silvioviscuso/ESP32-REACTJS-DEVKIT/Assets/1.png

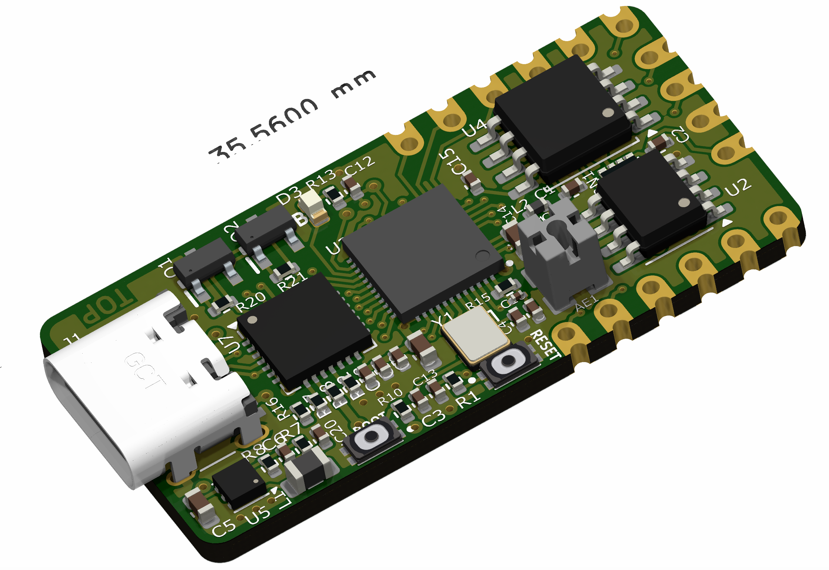
Assets/1.png
