silvioviscuso/ESP32-REACTJS-DEVKIT/Assets/Preview 2024-11-06 alle 11.11.40.png

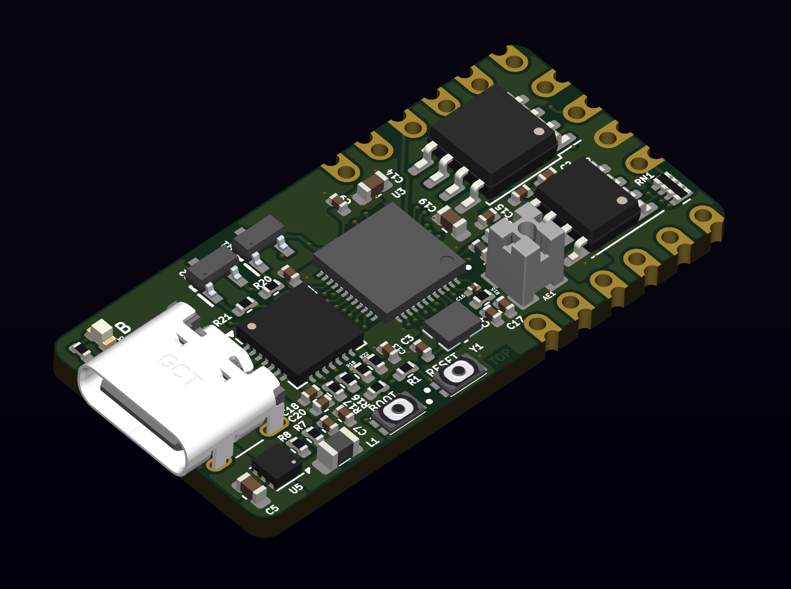
Assets/Preview 2024-11-06 alle 11.11.40.png
