silvioviscuso/ESP32-REACTJS-DEVKIT/Production data/PDF3D/V1.png

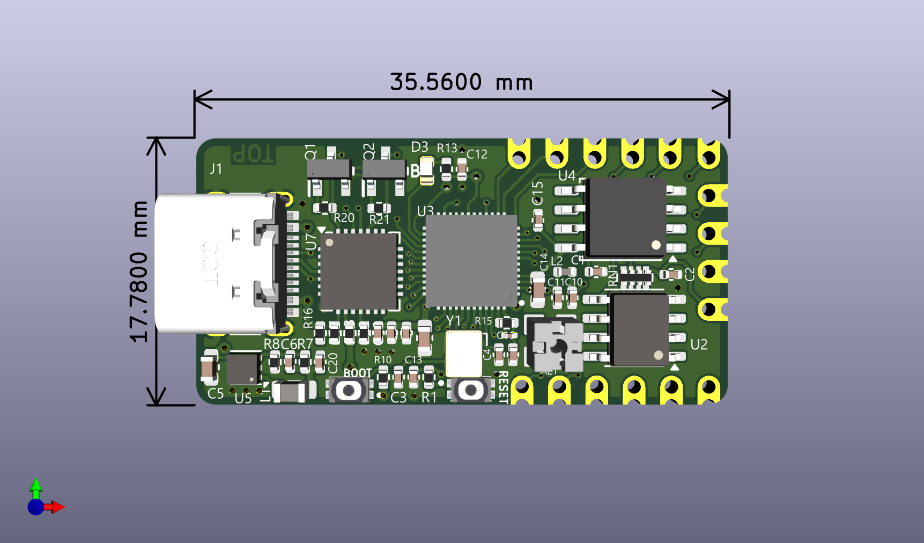
Production data/PDF3D/V1.png
