silvioviscuso/ESP32-REACTJS-DEVKIT/Production data/PDF3D/V1_back.png

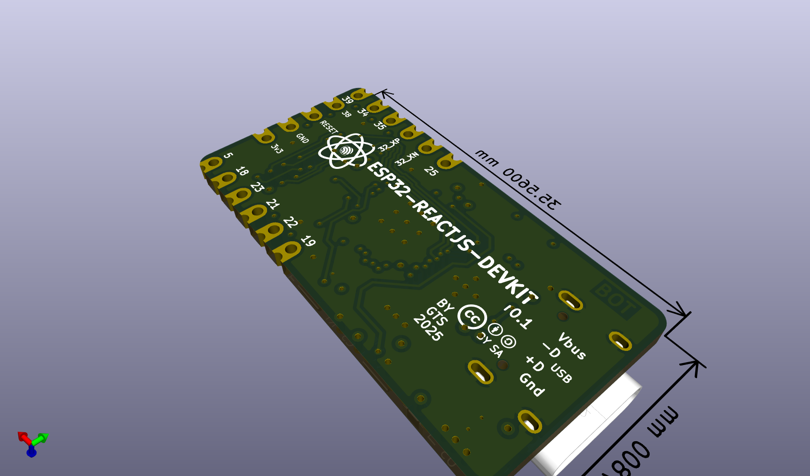
Production data/PDF3D/V1_back.png
