silvioviscuso/ESP32-REACTJS-DEVKIT/ESP32-DOWDQ6-16MB-BOILERPLATE-SCH/Boilerplate_esp-dowdq6_sch/Boilerplate_esp-dowdq6_sch.kicad_sch

## KiCad design ESP32-DOWDQ6-16MB-BOILERPLATE-SCH/Boilerplate_esp-dowdq6_sch/Boilerplate_esp-dowdq6_sch.kicad_sch (2024-12-04)

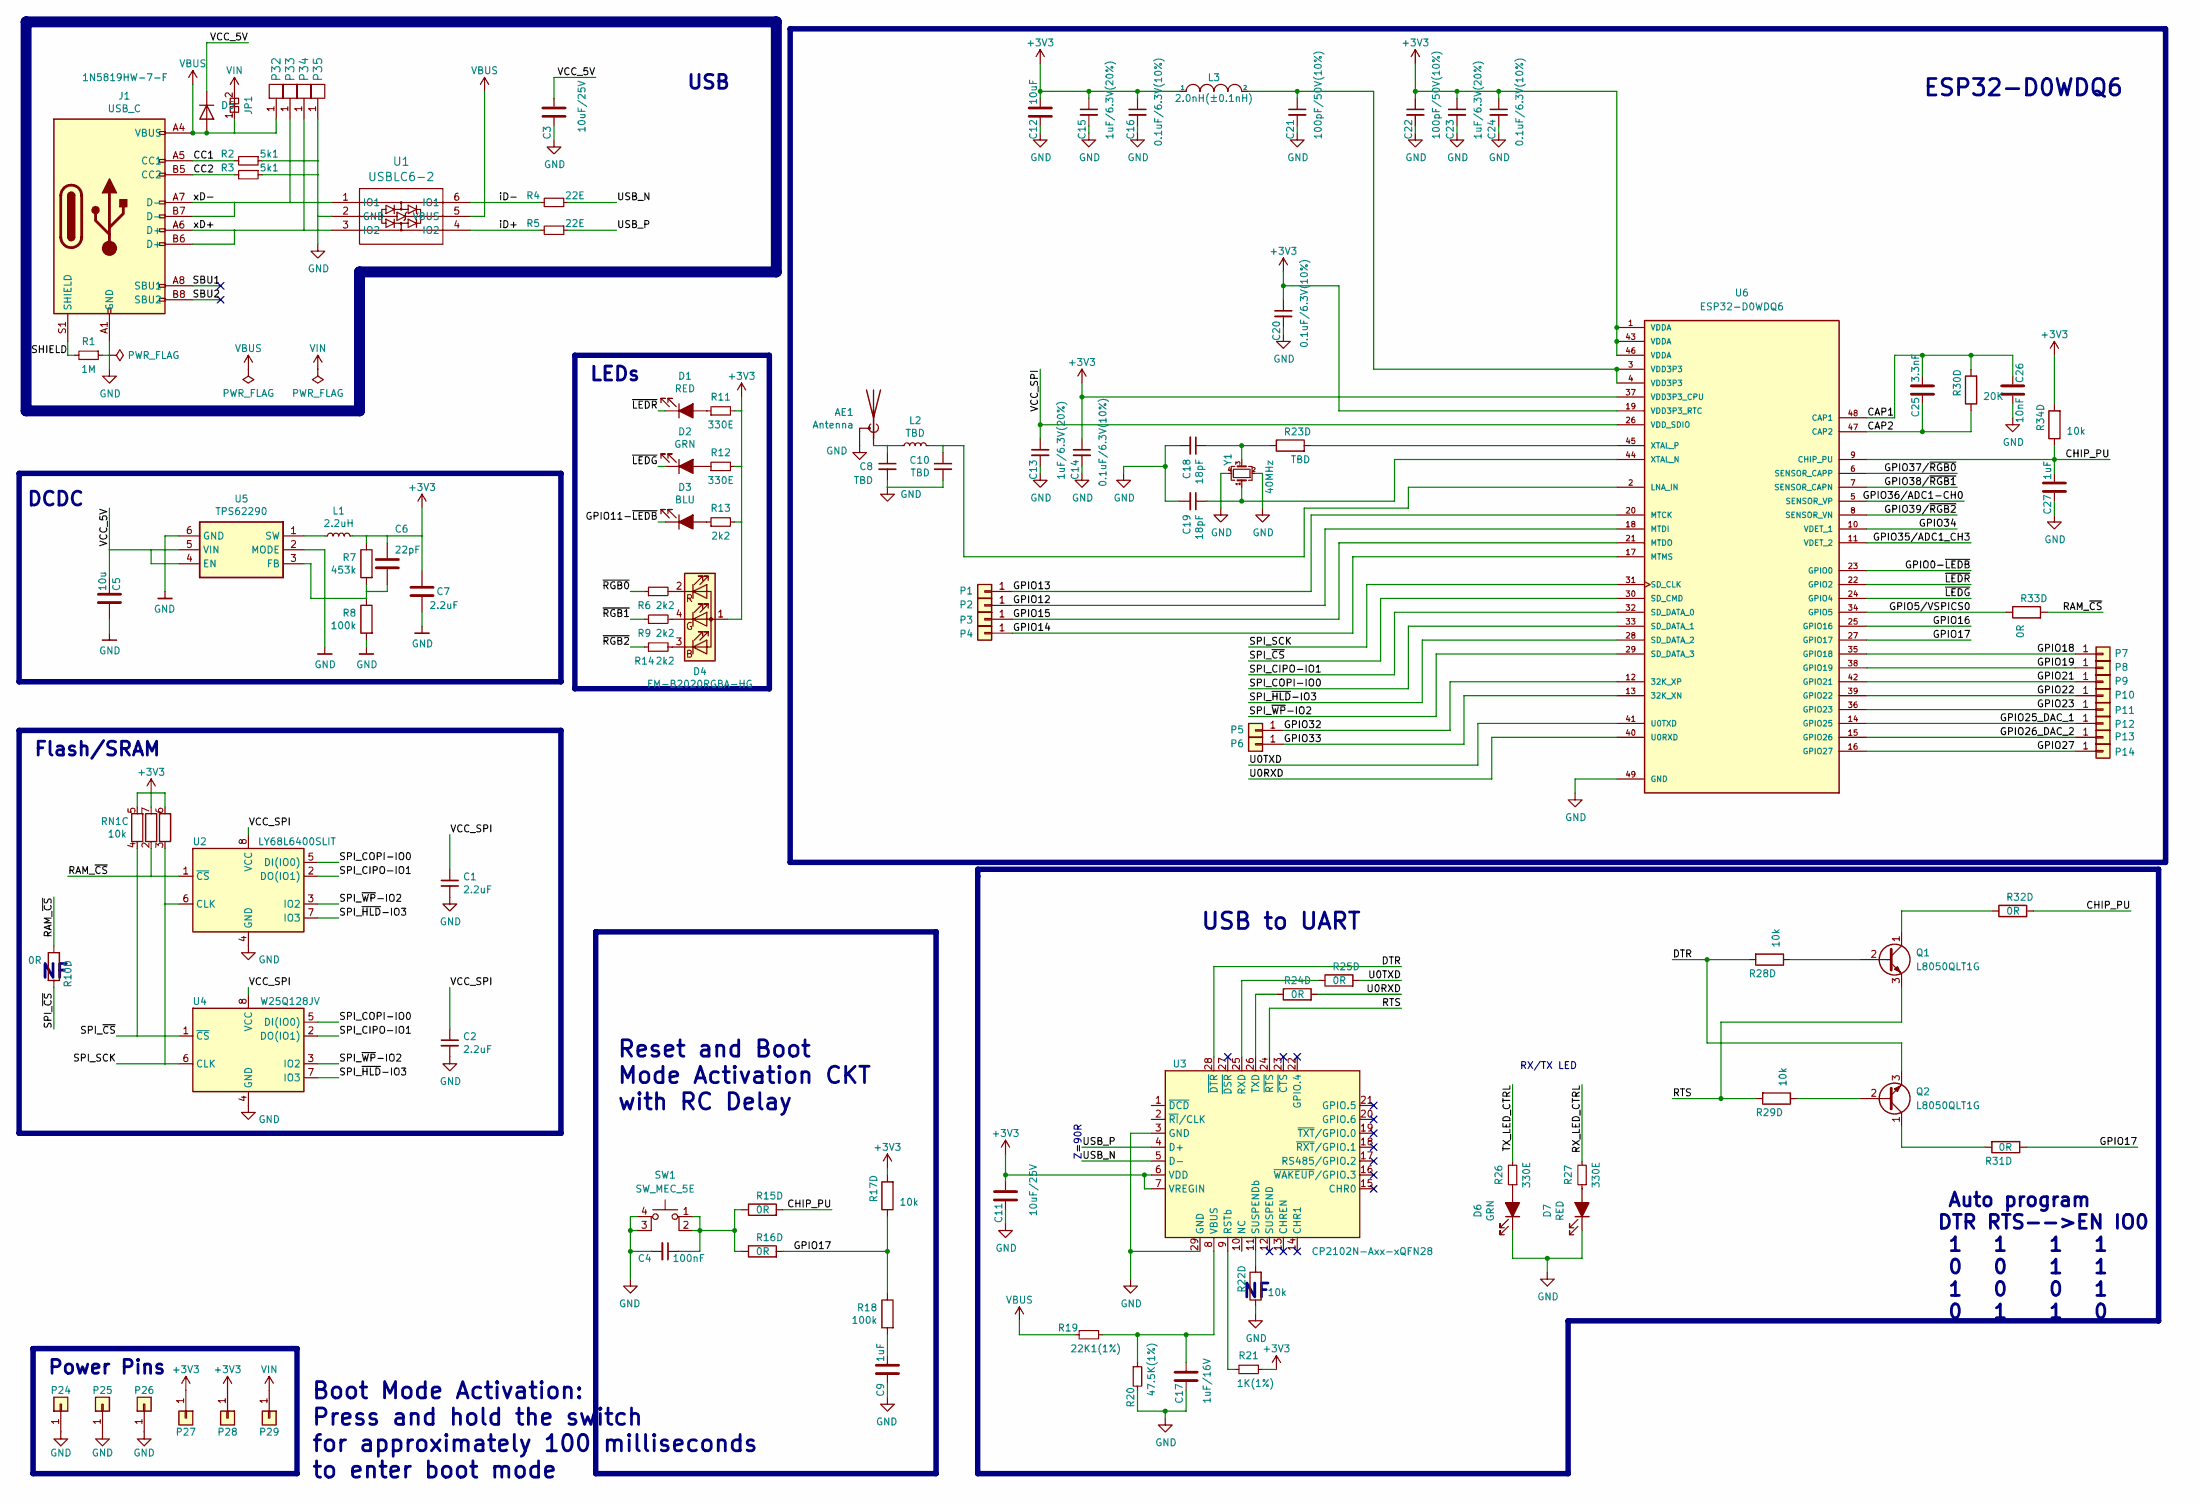
[picture p29: schematic Boilerplate_esp-dowdq6_sch.kicad_sch]

Parts:
AE1: Antenna; 0479480001
C1, C2, C7: 2.2uF; C_0402_1005Metric
C3, C11: 10uF/25V; C_0603_1608Metric
C4: 100nF; C_0402_1005Metric
C5: 10u; C_0603_1608Metric
C6: 22pF; C_0402_1005Metric
C8, C10: TBD; C_0402_1005Metric
C9, C27: 1uF; C_0603_1608Metric
C12: 10uF; C_0603_1608Metric
C13, C15, C23: 1uF/6.3V(20%); C_0402_1005Metric
C14, C16, C20, C24: 0.1uF/6.3V(10%); C_0402_1005Metric
C17: 1uF/16V; C_0603_1608Metric
C18, C19: 18pF; C_0402_1005Metric
C21, C22: 100pF/50V(10%); C_0402_1005Metric
C25: 3.3nF; C_0603_1608Metric
C26: 10nF; C_0603_1608Metric
D1, D7: RED; LED_0603_1608Metric_Compact
D2, D6: GRN; LED_0603_1608Metric_Compact
D3: BLU; LED_0603_1608Metric_Compact
D4: FM-B2020RGBA-HG; LED_Lumex_SML-LX0303SIUPGUSB
D5: 1N5819HW-7-F; D_SOD-123
J1: USB_C; USB_C_Receptacle_HRO_TYPE-C-31-M-12
JP1: Jumper; SolderJumper-2_P1.3mm_Bridged2Bar_RoundedPad1.0x1.5mm
L1: 2.2uH; L_0805_2012Metric
L2: TBD; L_0402_1005Metric
L3: 2.0nH(±0.1nH); L_0402_1005Metric
P1: 4; Pin_Header_Straight_Round_1x01_Castellated
P2: 5; Pin_Header_Straight_Round_1x01_Castellated
P3: 6; Pin_Header_Straight_Round_1x01_Castellated
P4: 7; Pin_Header_Straight_Round_1x01_Castellated
P5: 20; Pin_Header_Straight_Round_1x01_Castellated
P6: 21; Pin_Header_Straight_Round_1x01_Castellated
P7: 3; Pin_Header_Straight_Round_1x01_Castellated
P8: 1; Pin_Header_Straight_Round_1x01_Castellated
P9: 0; Pin_Header_Straight_Round_1x01_Castellated
P10: 2; Pin_Header_Straight_Round_1x01_Castellated
P11: 8; Pin_Header_Straight_Round_1x01_Castellated
P12: 10; Pin_Header_Straight_Round_1x01_Castellated
P13: 23; Pin_Header_Straight_Round_1x01_Castellated
P14: 22; Pin_Header_Straight_Round_1x01_Castellated
P24, P25, P26: GND; Pin_Header_Straight_Round_1x01_Castellated
P27, P28: 3V3; Pin_Header_Straight_Round_1x01_Castellated
P29: VIN; Pin_Header_Straight_Round_1x01_Castellated
P32, P33, P34, P35: UP; PAD_SMD_1x2.65_ROUNDED
Q1, Q2: L8050QLT1G; TO-92_Inline
R1: 1M; R_0402_1005Metric
R2, R3: 5k1; R_0402_1005Metric
R4, R5: 22E; R_0402_1005Metric
R6, R9, R13, R14: 2k2; R_0402_1005Metric
R7: 453k; R_0402_1005Metric
R8, R18: 100k; R_0402_1005Metric
R10, R15, R16, R24, R25, R31, R32, R33: 0R; R_0402_1005Metric
R11, R12, R26, R27: 330E; R_0402_1005Metric
R17, R22, R28, R29, R34: 10k; R_0402_1005Metric
R19: 22K1(1%); R_0603_1608Metric
R20: 47.5K(1%); R_0402_1005Metric
R21: 1K(1%); R_0402_1005Metric
R23: TBD; R_0402_1005Metric
R30: 20K; R_0402_1005Metric
RN1: 10k; R_0402_1005Metric
SW1: SW_MEC_5E; SW_Push_1P1T_NO_6x6mm_H9.5mm
U1: USBLC6-2; SOT-666
U2: LY68L6400SLIT; SOIC-8_3.9x4.9mm_P1.27mm
U3: CP2102N-Axx-xQFN28; QFN-28-1EP_5x5mm_P0.5mm_EP3.35x3.35mm
U4: W25Q128JV; SOIC-8_5.23x5.23mm_P1.27mm
U5: TPS62290; WSON-6-1EP_2x2mm_P0.65mm_EP1x1.6mm_ThermalVias
U6: ESP32-D0WDQ6
Y1: 40MHz; Crystal_SMD_Abracon_ABM10-4Pin_2.5x2.0mm

Connections:
+3V3: C6.1, C7.1, C11.1, C12.1, C14.1, C15.1, C16.1, C20.1, C22.1, C23.1, C24.1, D4.1 (A), L1.2, L3.1, P27.1, P28.1, R7.1, R11.2, R12.2, R13.2, R17.5 (R4.2), R21.1, R34.5 (R4.2), RN1.5 (R4.2), RN1.6 (R3.2), RN1.7 (R2.2), U3.6 (VDD), U3.7 (VREGIN), U6.1 (VDDA), U6.19 (VDD3P3_RTC), U6.37 (VDD3P3_CPU), U6.43 (VDDA), U6.46 (VDDA)
CAP1: C25.1, C26.2, R30.5 (R4.2), U6.48 (CAP1)
CAP2: C25.2, R30.4 (R4.1), U6.47 (CAP2)
CC1: J1.A5 (CC1), R2.2
CC2: J1.B5 (CC2), R3.2
CHIP_PU: C27.1, R15.5 (R4.2), R32.5 (R4.2), R34.4 (R4.1), U6.9 (CHIP_PU)
DTR: Q2.3 (E), R28.5 (R4.2), U3.28 (~DTR)
GND: AE1.2 (Shield), C1.2, C2.2, C3.2, C4.2, C5.2, C7.2, C8.2, C9.2, C10.2, C11.2, C12.2, C13.2, C14.2, C15.2, C16.2, C17.2, C18.2, C19.2, C20.2, C21.2, C22.2, C23.2, C24.2, C26.1, C27.2, D6.1 (K), D7.1 (K), J1.A1 (GND), J1.A12 (GND), J1.B1 (GND), J1.B12 (GND), P24.1, P25.1, P26.1, P35.1, R1.1, R2.1, R3.1, R8.2, R20.2, R22.4 (R4.1), SW1.3 (K), SW1.4 (A), U1.2 (GND), U2.4 (GND), U3.3 (GND), U3.29 (GND), U4.4 (GND), U5.2 (MODE), U5.6 (GND), U5.7 (GND), U6.49 (GND), Y1.2, Y1.4
GPIO0-~LEDB: U6.23 (GPIO0)
GPIO5/VSPICS0: R33.4 (R4.1), U6.34 (GPIO5)
GPIO11-~LEDB: D3.1 (K)
GPIO12: P2.1, U6.18 (MTDI)
GPIO13: P1.1, U6.20 (MTCK)
GPIO14: P4.1, U6.17 (MTMS)
GPIO15: P3.1, U6.21 (MTDO)
GPIO16: U6.25 (GPIO16)
GPIO17: R16.5 (R4.2), R17.4 (R4.1), R18.1, R31.4 (R4.1), U6.27 (GPIO17)
GPIO18: P7.1, U6.35 (GPIO18)
GPIO19: P8.1, U6.38 (GPIO19)
GPIO21: P9.1, U6.42 (GPIO21)
GPIO22: P10.1, U6.39 (GPIO22)
GPIO23: P11.1, U6.36 (GPIO23)
GPIO25_DAC_1: P12.1, U6.14 (GPIO25)
GPIO26_DAC_2: P13.1, U6.15 (GPIO26)
GPIO27: P14.1, U6.16 (GPIO27)
GPIO32: P5.1, U6.12 (32K_XP)
GPIO33: P6.1, U6.13 (32K_XN)
GPIO34: U6.10 (VDET_1)
GPIO35/ADC1_CH3: U6.11 (VDET_2)
GPIO36/ADC1-CH0: U6.5 (SENSOR_VP)
GPIO37/~RGB0: U6.6 (SENSOR_CAPP)
GPIO38/~RGB1: U6.7 (SENSOR_CAPN)
GPIO39/~RGB2: U6.8 (SENSOR_VN)
unnamed: AE1.1 (A), C8.1, L2.2
unnamed: C4.1, R15.4 (R4.1), R16.4 (R4.1), SW1.1, SW1.2
unnamed: C6.2, R7.2, R8.1, U5.3 (FB)
unnamed: C9.1, R18.2
unnamed: C10.1, L2.1, U6.2 (LNA_IN)
unnamed: C17.1, R19.1, R20.1, U3.8 (VBUS)
unnamed: C18.1, R23.4 (R4.1), Y1.3
unnamed: C19.1, U6.44 (XTAL_N), Y1.1
unnamed: C21.1, L3.2, U6.3 (VDD3P3), U6.4 (VDD3P3)
unnamed: D1.2 (A), R11.1
unnamed: D2.2 (A), R12.1
unnamed: D3.2 (A), R13.1
unnamed: D4.2 (RK), R6.2
unnamed: D4.3 (BK), R14.2
unnamed: D4.4 (GK), R9.2
unnamed: D6.2 (A), R26.1
unnamed: D7.2 (A), R27.1
unnamed: L1.1, U5.1 (SW)
unnamed: Q1.1 (C), R32.4 (R4.1)
unnamed: Q1.2 (B), R28.4 (R4.1)
unnamed: Q2.1 (C), R31.5 (R4.2)
unnamed: Q2.2 (B), R29.4 (R4.1)
unnamed: R21.2, U3.9 (RSTb)
unnamed: R22.5 (R4.2), U3.11 (SUSPENDb)
unnamed: R23.5 (R4.2), U6.45 (XTAL_P)
unnamed: R24.4 (R4.1), U3.26 (TXD)
unnamed: R25.4 (R4.1), U3.25 (RXD)
RAM_~CS: R10.4 (R4.1), R33.5 (R4.2), RN1.2 (R2.1), U2.1 (~CS)
RTS: Q1.3 (E), R29.5 (R4.2), U3.24 (~RTS)
RX_LED_CTRL: R27.2
SBU1: J1.A8 (SBU1)
SBU2: J1.B8 (SBU2)
SHIELD: J1.S1 (SHIELD), R1.2
SPI_CIPO-IO1: U2.2 (DO(IO1)), U4.2 (DO(IO1)), U6.32 (SD_DATA_0)
SPI_COPI-IO0: U2.5 (DI(IO0)), U4.5 (DI(IO0)), U6.33 (SD_DATA_1)
SPI_SCK: RN1.3 (R3.1), U2.6 (CLK), U4.6 (CLK), U6.31 (SD_CLK)
SPI_~CS: R10.5 (R4.2), RN1.4 (R4.1), U4.1 (~CS), U6.30 (SD_CMD)
SPI_~HLD-IO3: U2.7 (IO3), U4.7 (IO3), U6.28 (SD_DATA_2)
SPI_~WP-IO2: U2.3 (IO2), U4.3 (IO2), U6.29 (SD_DATA_3)
TX_LED_CTRL: R26.2
U0RXD: R24.5 (R4.2), U6.40 (U0RXD)
U0TXD: R25.5 (R4.2), U6.41 (U0TXD)
USB_N: R4.1, U3.5 (D-)
USB_P: R5.1, U3.4 (D+)
VBUS: D5.2 (A), J1.A4 (VBUS), J1.A9 (VBUS), J1.B4 (VBUS), J1.B9 (VBUS), JP1.1, P32.1, R19.2, U1.5 (VBUS)
VCC_5V: C3.1, C5.1, D5.1 (K), U5.4 (EN), U5.5 (VIN)
VCC_SPI: C1.1, C2.1, C13.1, U2.8 (VCC), U4.8 (VCC), U6.26 (VDD_SDIO)
VIN: JP1.2, P29.1
iD+: R5.2, U1.4 (IO2)
iD-: R4.2, U1.6 (IO1)
xD+: J1.A6 (D+), J1.B6 (D+), P34.1, U1.3 (IO2)
xD-: J1.A7 (D-), J1.B7 (D-), P33.1, U1.1 (IO1)
~LEDG: D2.1 (K), U6.24 (GPIO4)
~LEDR: D1.1 (K), U6.22 (GPIO2)
~RGB0: R6.1
~RGB1: R9.1
~RGB2: R14.1

Notes on the sheet:
Reset and Boot Mode Activation CKT with RC Delay
USB to UART
DCDC
Flash/SRAM
Boot Mode Activation: Press and hold the switch for approximately 100 milliseconds to enter boot mode
Z=90R
Power Pins
ESP32-D0WDQ6
Auto program DTR RTS-->EN IO0 1 1 1 1 0 0 1 1 1 0 0 1 0 1 1 0
LEDs
USB
RX/TX LED
